Yarnadori/RP-ROM/software/board.h

/*
 * Copyright (c) 2020 Raspberry Pi (Trading) Ltd.
 *
 * SPDX-License-Identifier: BSD-3-Clause
 */

// -----------------------------------------------------
// NOTE: THIS HEADER IS ALSO INCLUDED BY ASSEMBLER SO
//       SHOULD ONLY CONSIST OF PREPROCESSOR DIRECTIVES
// -----------------------------------------------------

// This header may be included by other board headers as "board.h"

// pico_cmake_set PICO_PLATFORM=rp2350

#ifndef _BOARDS_RP_ROM_H
#define _BOARDS_RP_ROM_H

// For board detection
#define YAMADORI_RP_ROM

// --- RP2350 VARIANT ---
#define PICO_RP2350A 1

// --- LED ---
#ifndef PICO_DEFAULT_LED_PIN
#define PICO_DEFAULT_LED_PIN 12
#endif

// --- FLASH ---
#define PICO_BOOT_STAGE2_CHOOSE_W25Q080 1

#ifndef PICO_FLASH_SPI_CLKDIV
#define PICO_FLASH_SPI_CLKDIV 3
#endif

// pico_cmake_set_default PICO_FLASH_SIZE_BYTES = (2 * 1024 * 1024)
#ifndef PICO_FLASH_SIZE_BYTES
#define PICO_FLASH_SIZE_BYTES (2 * 1024 * 1024)
#endif

// pico_cmake_set_default PICO_RP2350_A2_SUPPORTED = 1
#ifndef PICO_RP2350_A2_SUPPORTED
#define PICO_RP2350_A2_SUPPORTED 1
#endif

#endif
